RAMilewski/SparkStudioSalem-IndustrialLaserCutters/stl/LaserCutterParts-P_ReedSwitch_Magnet.stl

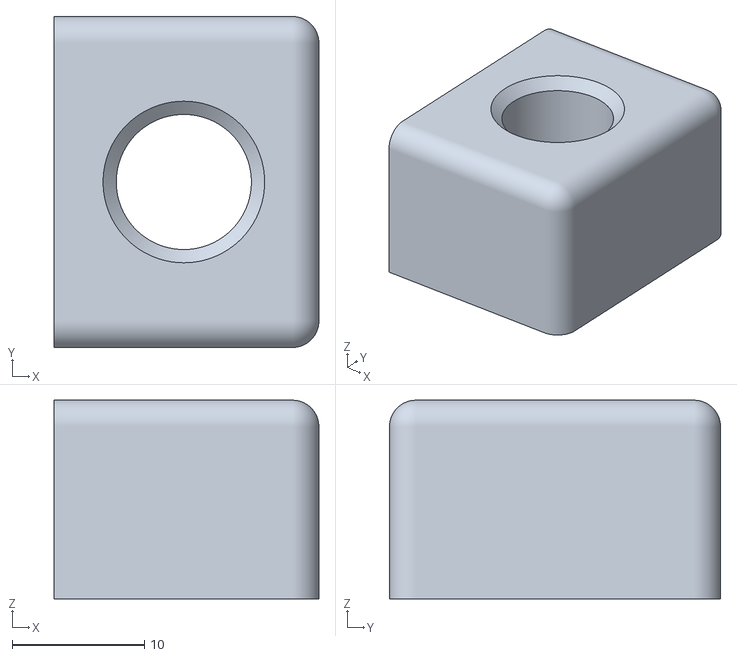
[picture p15: CAD file, 2026-03-23]
stl/LaserCutterParts-P_ReedSwitch_Magnet.stl
20.0 x 25.0 x 15.0
