RAMilewski/SparkStudioSalem-IndustrialLaserCutters/stl/LaserCutterParts-P_AlignmentWrench2_5mm.stl

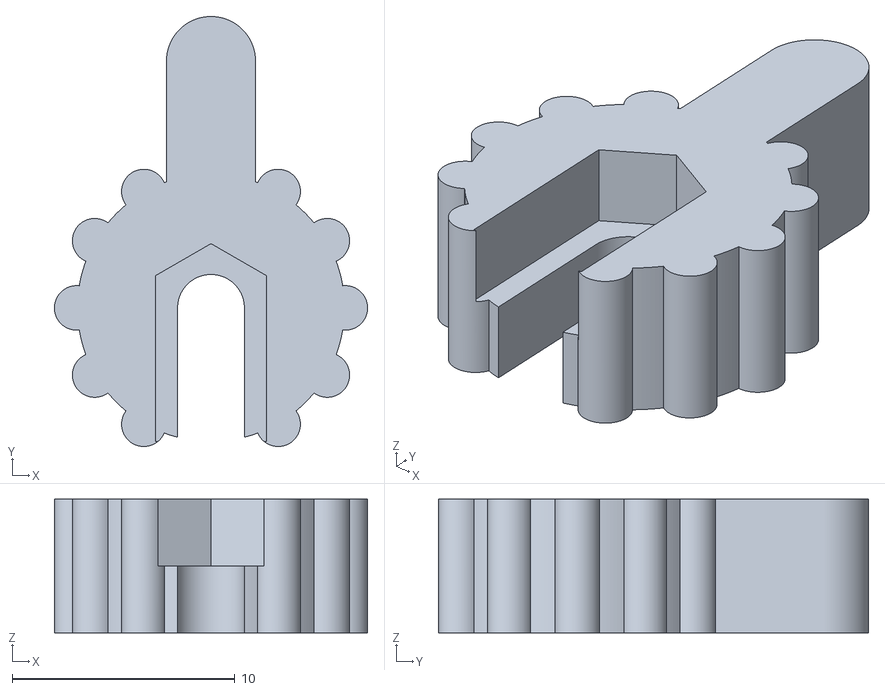
[picture p16: CAD file, 2026-03-23]
stl/LaserCutterParts-P_AlignmentWrench2_5mm.stl
14.1 x 19.3 x 6.00
