RAMilewski/SparkStudioSalem-IndustrialLaserCutters/stl/LaserCutterParts-P_PowerBox_Body.stl

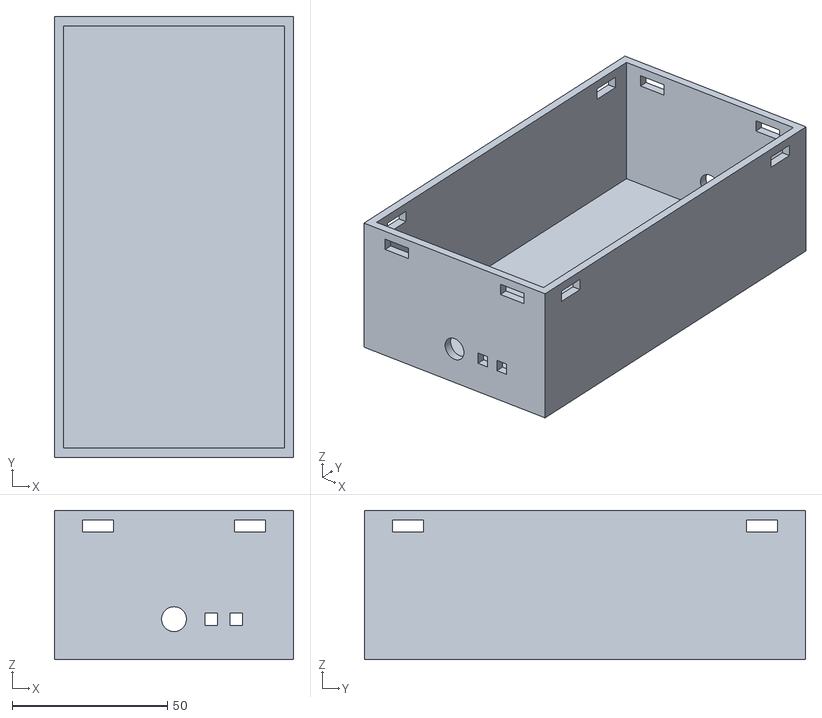
[picture p17: CAD file, 2026-03-23]
stl/LaserCutterParts-P_PowerBox_Body.stl
77.0 x 142.0 x 48.0
