RAMilewski/SparkStudioSalem-IndustrialLaserCutters/stl/LaserCutterParts-P_TPLinkBracket_Left.stl

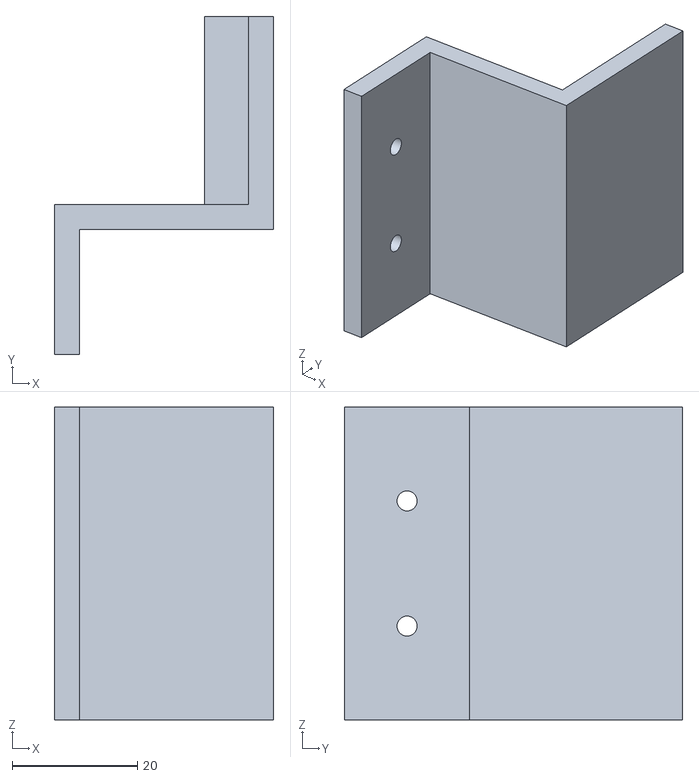
[picture p18: CAD file, 2026-03-23]
stl/LaserCutterParts-P_TPLinkBracket_Left.stl
35.0 x 54.0 x 50.0
