RAMilewski/SparkStudioSalem-IndustrialLaserCutters/stl/LaserCutterParts-P_ReedSwitch_Holder.stl

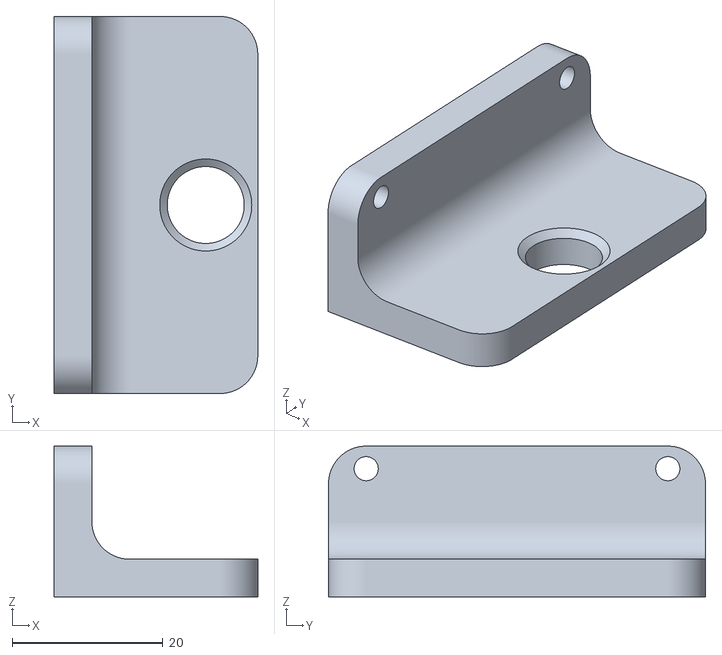
[picture p19: CAD file, 2026-03-23]
stl/LaserCutterParts-P_ReedSwitch_Holder.stl
27.0 x 50.0 x 20.0
