RAMilewski/SparkStudioSalem-IndustrialLaserCutters/stl/LaserCutterParts-P_AlignmentWrench2_4_9mm.stl

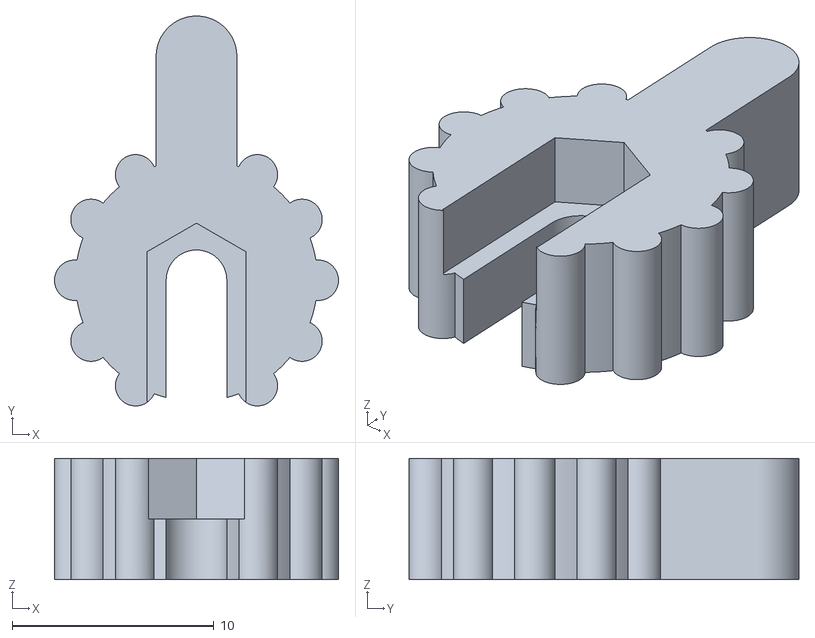
[picture p20: CAD file, 2026-03-23]
stl/LaserCutterParts-P_AlignmentWrench2_4_9mm.stl
14.1 x 19.3 x 6.00
