RAMilewski/SparkStudioSalem-IndustrialLaserCutters/stl/LaserCutterParts-P_PowerBox_Lid.stl

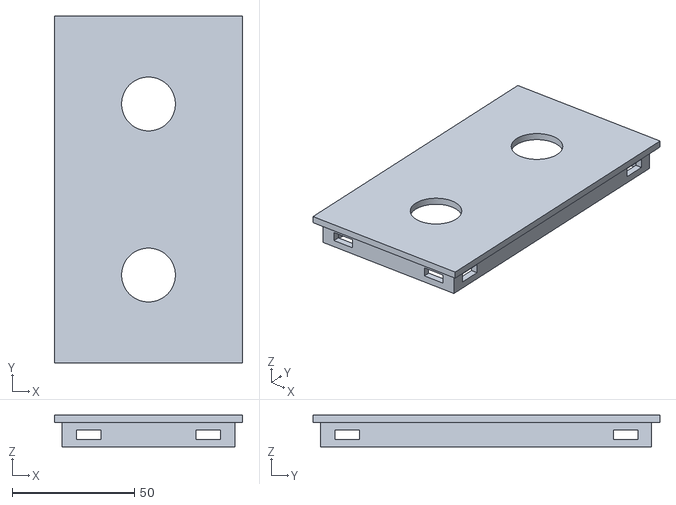
[picture p21: CAD file, 2026-03-23]
stl/LaserCutterParts-P_PowerBox_Lid.stl
77.0 x 142.0 x 13.0
