RAMilewski/SparkStudioSalem-IndustrialLaserCutters/stl/LaserCutterParts-P_HolePlug_FrontPanelsTester.stl

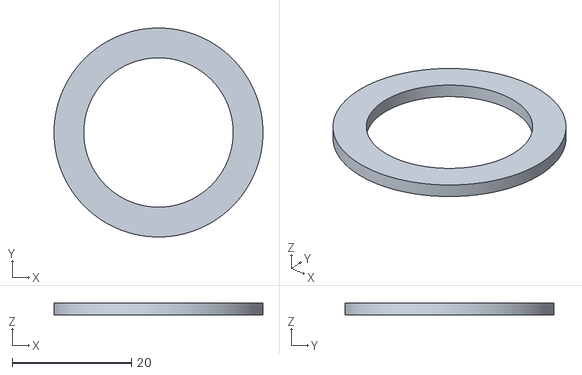
[picture p22: CAD file, 2026-03-23]
stl/LaserCutterParts-P_HolePlug_FrontPanelsTester.stl
35.0 x 35.0 x 2.00
