RAMilewski/SparkStudioSalem-IndustrialLaserCutters/stl/LaserCutterParts-P_TPLinkBracket.stl

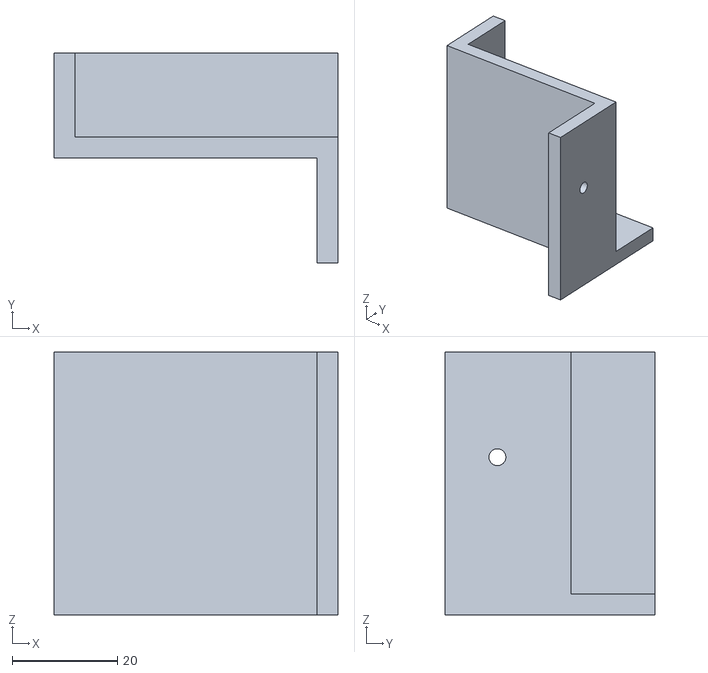
[picture p23: CAD file, 2026-03-23]
stl/LaserCutterParts-P_TPLinkBracket.stl
54.0 x 40.0 x 50.0
