RAMilewski/SparkStudioSalem-IndustrialLaserCutters/stl/LaserCutterParts-P_Endcap.stl

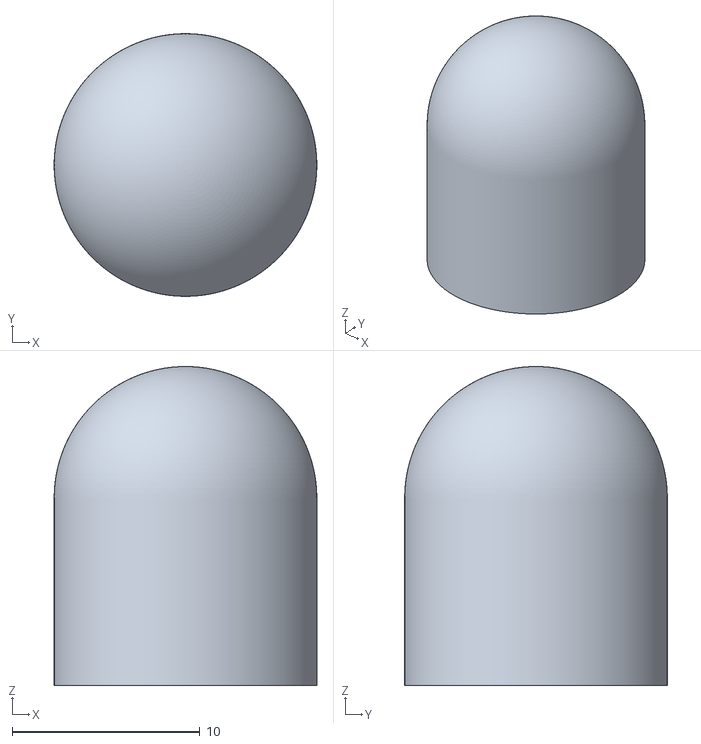
[picture p24: CAD file, 2026-03-23]
stl/LaserCutterParts-P_Endcap.stl
14.0 x 14.0 x 17.0
