RAMilewski/SparkStudioSalem-IndustrialLaserCutters/stl/LaserCutterParts-P_LimitSwitch_Switch.stl

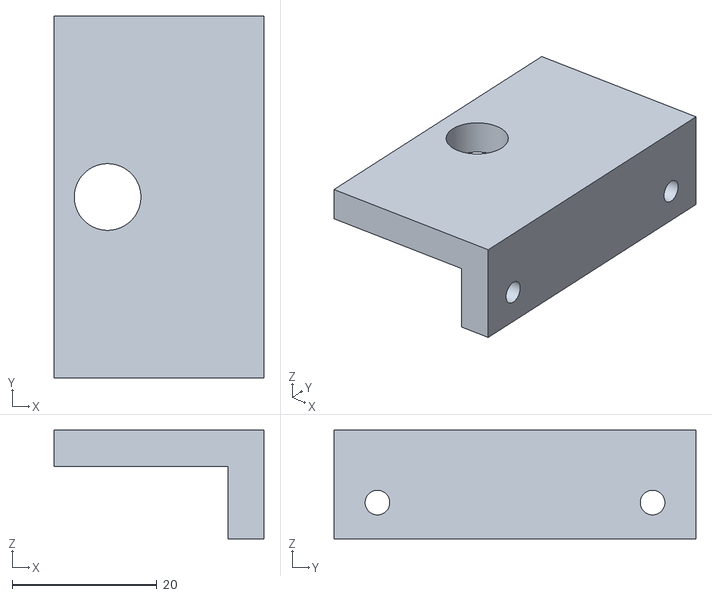
[picture p25: CAD file, 2026-03-23]
stl/LaserCutterParts-P_LimitSwitch_Switch.stl
29.0 x 50.0 x 15.0
