RAMilewski/SparkStudioSalem-IndustrialLaserCutters/space/network-topology.kicad_sch

## KiCad design space/network-topology.kicad_sch (2026-03-25)

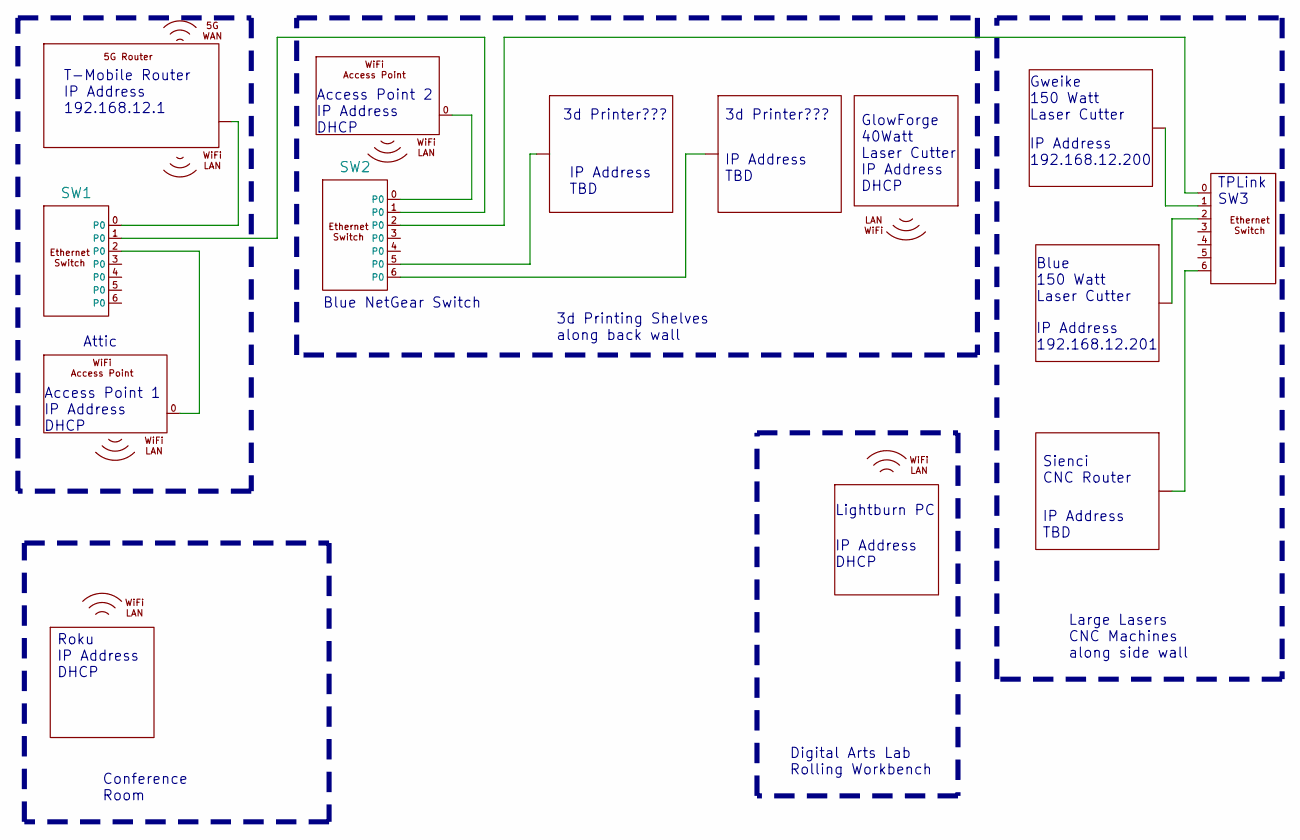
[picture p34: schematic network-topology.kicad_sch]

Parts:
SW1, SW2: (no value)
U1, U2, U3, U4, U5, U6, U7, U8, U9, U10, U12: (no value)
UX: (no value)

Connections:
unnamed: SW1.0, U1.
unnamed: SW1.1, SW2.1
unnamed: SW1.2, U2.0
unnamed: SW2.0, U3.0
unnamed: SW2.2, U12.0
unnamed: SW2.5, U8.
unnamed: SW2.6, U7.
unnamed: U4., U12.1
unnamed: U5., U12.2
unnamed: U6., U12.6

Notes on the sheet:
IP Address 192.168.12.201
Roku IP Address DHCP
Lightburn PC
3d Printing Shelves along back wall
3d Printer???
Large Lasers CNC Machines along side wall
Gweike 150 Watt Laser Cutter
IP Address TBD
Attic
Digital Arts Lab Rolling Workbench
IP Address DHCP
IP Address 192.168.12.200
Access Point 2 IP Address DHCP
GlowForge 40Watt Laser Cutter IP Address DHCP
TPLink SW3
T-Mobile Router IP Address 192.168.12.1
Blue 150 Watt Laser Cutter
Conference Room
Blue NetGear Switch
Access Point 1 IP Address DHCP
Sienci CNC Router
